maxmacstn/iPod-Classic-6-mods/Captures/ipod-i2s-line.jpg

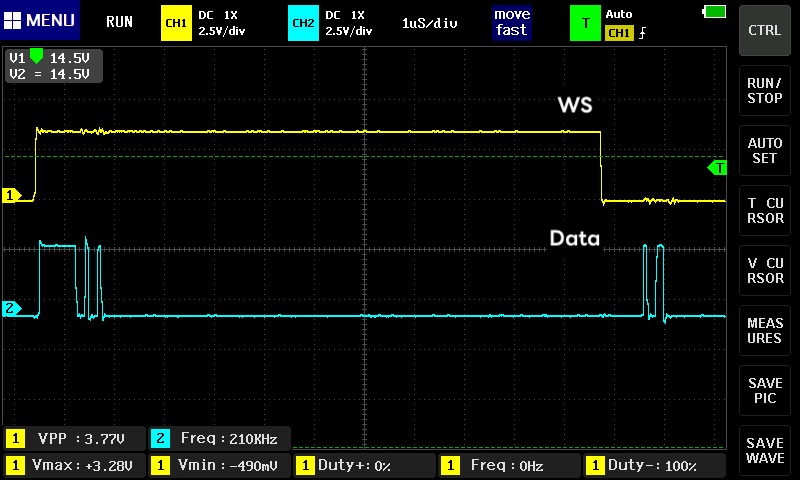
Captures/ipod-i2s-line.jpg
