maxmacstn/iPod-Classic-6-mods/Captures/iPod_i2s_conf.jpg

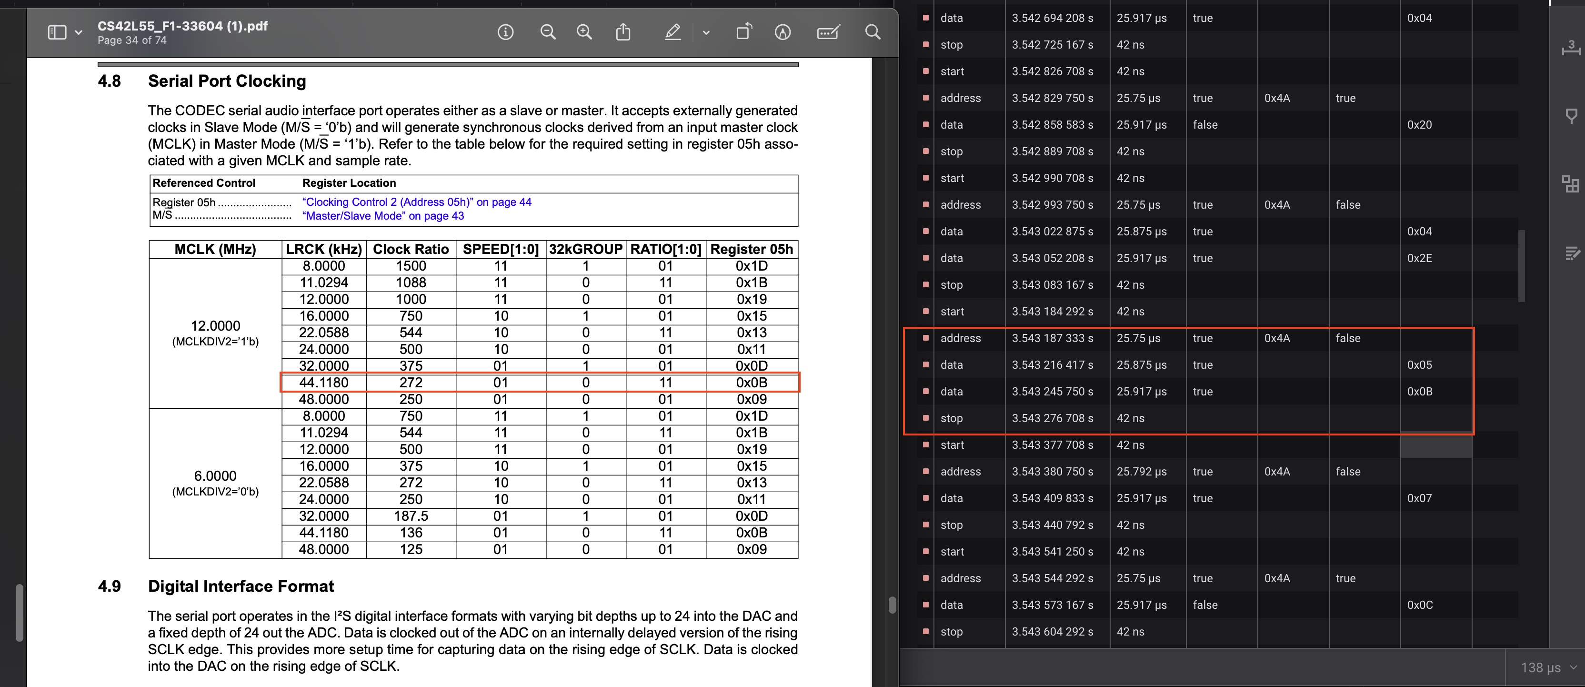
Captures/iPod_i2s_conf.jpg
