maxmacstn/iPod-Classic-6-mods/Captures/iPod_i2s_conf_2.jpg

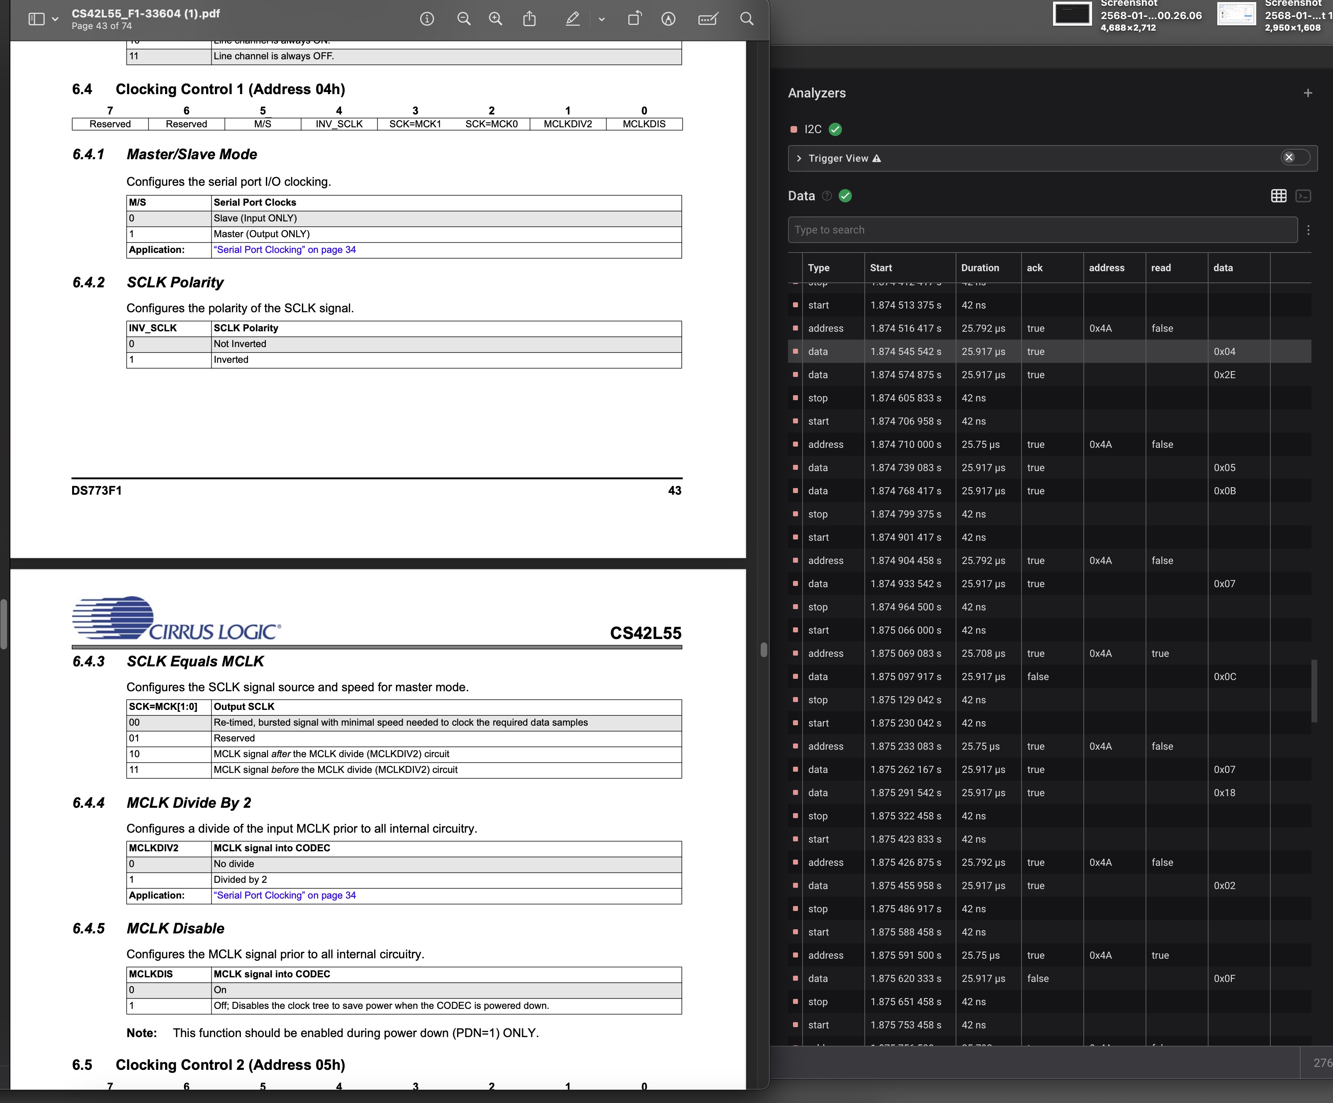
Captures/iPod_i2s_conf_2.jpg
