maxmacstn/iPod-Classic-6-mods/Captures/IPOD_WORD.jpg

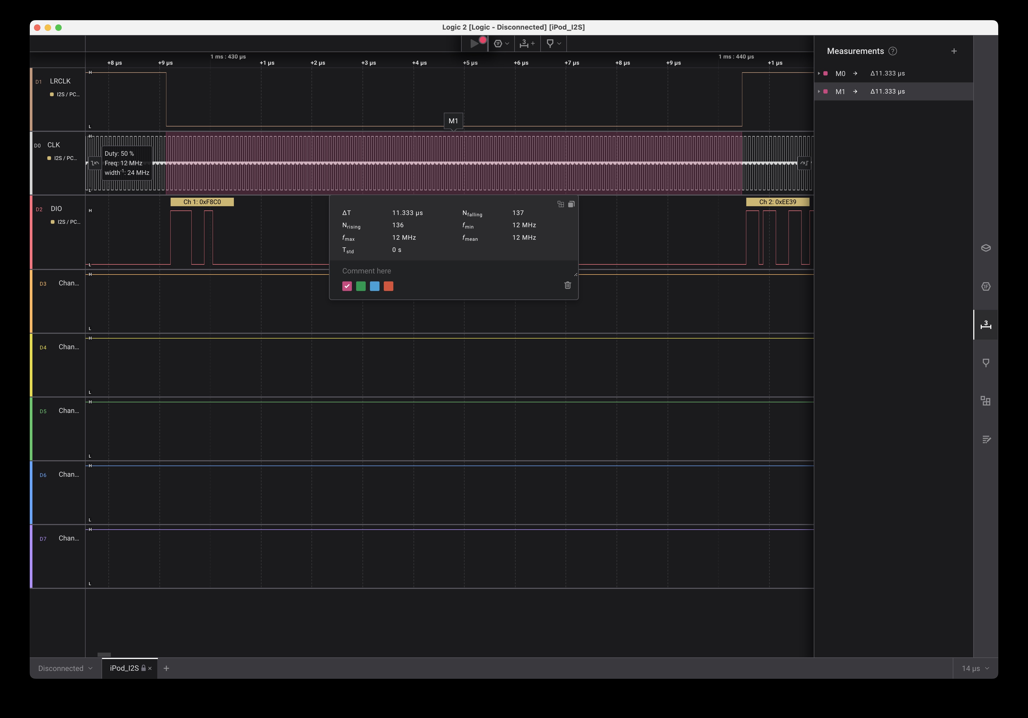
Captures/IPOD_WORD.jpg
